RarceD/TFM--Bluetooth-Beacon-Tracking-/Technical project/Memmory/rarced_memmory.pdf

DOCUMENTO TÉCNICO

## SISTEMAS DE POSICIONAMIENTO DE OBJETOS MEDIANTE LA TECNOLOGÍA

## BLUETOOTH LOW ENERGY, MODO BEACON

27 de enero de 2021

Rubén Arce Domingo
Máster en automatización y robótica industrial
akimbo170@gmail.com

### Índice

1 Memoria descriptiva | 5
2 Memoria justificativa | 13
3 Planos | 21
4 Pliego de condiciones | 22
5 Presupuestos | 23
6 Bibliografía | 25

3

### Índice de figuras

1 | Detección de personas aplicando redes wifi | | 7
2 | Trama de bytes de cabecera de modo iBeacon (Apple) | | 8
3 | Modo Beacon Edison (Google) | | 9
4 | Diagrama explicativo de una red de ESP32 | 11
5 | Diagrama de GANTT del proyecto | 13
6 | Prueba de campo, medición Rssi de Beacons a 2 y 3 metros | 15
7 | Variaciones de Rssi entre beacons a distancias iguales | 16
8 | Trilataración con tres equipos escuchando al mismo Beacon | 16
9 | Posicionamiento de los beacons en carros de supermercado | 17
10 | Diferencia entre antena de media o cuarto de λ | 19
11 | Tipos de antena en función del espectro de emisión | 20
12 | Tipos de antena durante las pruebas de campo | 21

4

1 MEMORIA DESCRIPTIVA

### 1. Memoria descriptiva

### 1.1. Antecedentes y objeto del proyecto

Este proyecto surge como respuesta a la necesidad de poder localizar un número elevado de equipos en constante movimiento con exactitud en un espacio cerrado.

Los objetivos principales son los siguientes:

1. Estudiar las distintas alternativas para llevar a cabo el tracking de objetos de una forma sencilla y sin requerir de una gran inversión.
2. Analizar las tecnologías existentes para la monitorización en interiores.
3. Estudiar del parámetro Rssi como medida de la potencia de una señal y cálculo de la distancia entre equipos.
4. Desarrollar un sistema de visualización a través de un mapa sobre el que situar los equipos en movimiento.
5. Diseñar un hardware específico para la aplicación requerida.
6. Programar tanto el equipo emisor como el receptor, así como del algoritmo de visualización.
7. Comprobar el rendimiento del equipo y llevar a cabo pruebas de campo.

Una vez fijado el alcance del proyecto se puede empezar a planificar el mismo y buscar la mejor solución posible, por ello surgen los siguientes objetivos derivados de los primeros para poder sacar el producto al mercado:

1. Fijar un precio muy competitivo.
2. Desarrollar un producto estándar y de fácil aplicación.
3. Facilitar una instalación sencilla por un usuario no técnico.
4. Conseguir un mantenimiento escaso o nulo.
5. Producto seguro y que esté preparado para superar los marcados UL (Underwri-ters Laboratories) y CE (Conformidad Europea) así como protecciones frente a electricidad estática.

### 1.2. Ámbito de aplicación

El tracking de objetos en espacios cerrados está incrementando su popularidad debido a que es una arma de publicidad muy poderosa que demandan los grandes centros comerciales para llevar a cabo estudios de marketing y poder analizar el comportamiento de sus clientes.

BLE Tracking - 2021 | 5 | Rubén Arce

1.3 Análisis de soluciones al tracking de objetos | 1 MEMORIA DESCRIPTIVA

El mayor nicho de mercado es aplicado a no tener que interactuar tocando los objetos, esto, teniendo en cuenta los tiempos que corren, es una necesidad de numerosas empresas privadas, ayuntamientos y empresas estatales.

A modo de resumen se engloban los principales ámbitos de aplicación de esta tecnología:

1. Marketing: Estudios de mercado y de necesidad de los clientes. Elaboración de un "heat map", o mapa de las zonas con más afluencia de gente.
2. Sanidad: Monitorización de pacientes en planta.
3. Seguridad: Únicamente los empleados con autorización y proximidad podrán llevar a cabo acciones, esto tiene sentido a la hora de no tener que dar a cada trabajador una llave que pueda replicarse.
4. Vandalismo: Conociendo la localización de los equipos dentro de un local cerrado, en el momento en el que se deja de situar un elemento en el mapa, se puede dar la voz de alarma ante un robo.
5. Propaganda y nueva forma de publicidad: Activar acciones en función de la localización en determinados puntos de interés permite llevar a otro nivel las ideas de los publicistas.

Vemos por tanto que hay numerosas aplicaciones y una alta demanda de este producto tecnológico, es por ello por lo que se procede a explorar cual es la forma más adecuada para llevarlo a cabo e implementarlo.

### 1.3. Análisis de soluciones al tracking de objetos

Se plantean dos problemáticas, en primer lugar se busca llevar a cabo el seguimiento de elementos en movimiento, y por otro lado, se ha de enviar esta información de alguna forma al sistema correspondiente para que lleve a cabo el análisis de los datos. Esta última acción es esencial en el proceso, es lo realmente interesante desde el punto de vista del cliente final de esta tecnología. En lo que respecta a la obtención de datos de posición relativa de objetos o personas se presentan las siguientes opciones:

### 1.3.1. Wifi

Llevar a cabo el tracking mediante la escucha de wifis es una posibilidad, para ello sería necesario que, inicialmente, se colocara un móvil en cada uno de los objetos a identificar. Esto es aceptable en el caso de monitorización de personas pero inasumible para objetos.

El procedimiento consistiría en llevar a cabo un barrido de direcciones MACs que generan los móviles cuando tienen el wifi activado, es decir que este sistema no funcionaría en el caso de que una persona lleve puestos los datos del móvil únicamente.

BLE Tracking - 2021 | 6 | Rubén Arce

1 MEMORIA DESCRIPTIVA | 1.3 Análisis de soluciones al tracking de objetos

Otra desventaja es el hecho de que al tener un equipo buscando wifis la información personal del propietario, es decir, localización, fecha, hora a la que se intentó conectar y dirección MAC que identifica y relaciona un móvil a una persona, queda expuesta. Se ha de tener en cuenta la política de privacidad vigente, la cual se incumpliría al emplear esta tecnología para llevar a cabo el tracking.


Figura 1: Detección de personas aplicando redes wifi.

La única solución al problema es que se ha de pedir permiso formal a la persona para poder llevar a cabo el tratamiento de sus datos, cosa que es dificil puesto que se desconoce quien va a llevar a cabo el uso del equipo.

El artículo 29 de privacidad de datos de la comunidad europea dice lo siguiente: “WiFi-tracking, depending on the circumstances and purposes of the data collection, such tracking under the GDPR is likely either to be subject to consent, or may only be performed if the personal data collected is anonymised”. Es por ello por lo que se tendrá en cuenta como opción aunque haya numerosos puntos en contra para implementar un sistema como este.

### 1.3.2. GPS

La tecnología por excelencia para llevar a cabo el seguimiento de objetos o personas es el GPS. La principal desventaja que presenta es el elevado consumo energético comparado con el wifi o el bluetooth.

Mantener un módulo GPS encendido y pretender llegar a una autonomía de años es a día de hoy imposible, es por ello por lo que existen dos opciones. O se emplea un teléfono móvil para llevarlo a cabo, cosa inviable si se intentan monitorizar objetos y no personas en movimiento, o el tiempo de refresco de los datos ha de ser muy lento, del orden de horas, cosa de nuevo inasumible para la aplicación que se presenta.

Por otro lado, se ha de tener en cuenta también el aumento de precio que supondría un módulo GPS sumado a la antena que lleva consigo de dimensiones nada despreciables. Consecuentemente, esta tecnología se tendrá en cuenta pero no es la más adecuada para la problemática presente.

BLE Tracking - 2021 | 7 | Rubén Arce

1.3 Análisis de soluciones al tracking de objetos | 1 MEMORIA DESCRIPTIVA

### 1.3.3. Bluetooth Low Energy - Beacon

La tecnología Bluetooth es un estándar industrial aplicado a conexiones inalámbricas que permite transferir grandes cantidades de información en distancias cortas a bajas velocidades. Puede ser enfocado a conexión punto a punto, o como es nuestro caso llevar a cabo una red de equipos que emiten en modo broadcast.

La potencia de emisión va desde los -20 dBm (0.01 mW) hasta los +20 dBm (100 mW). Cuanta mayor potencia de emisión, mayor consumo energético del dispositivo, pero también conseguiremos una mayor distancia de escaneo.

La forma de envío de datos que más encaja dentro de la tecnología BLE (Bluetooth Low Energy) es Beacon o baliza, un dispositivo que transmite una señal de bluetooth cada cierto tiempo y es visible por cualquier otro equipo que escuche en esa misma frecuencia. La principal ventaja es que no es necesario llevar a cabo la conexión al equipo que escucha. Existen varios tipos de beacons:

1. iBeacon: Fue la primera tecnología BLE Beacon desarrollada por Apple. Permite leer y emitir en modo broadcast para cualquier dispositivo que disponga de Bluetooth low energy. Es un protocolo propietario, es decir es un estándar cerrado. Los iBeacons disponen de los siguientes identificadores:

UUID: Indentificador único del dispositivo, una cadena de carácteres de 16 bytes que permite caracterizar a cada equipo.

Major: Número entero de 0 a 65535, se usa para identificar grupos, un ejemplo sería asignar un Major común para todos los beacons de una misma planta o habitación.

Minor: Es también un número entero de 0 a 65535 que se emplea para distinguir un Beacon específico dentro de un grupo, entendiéndose como grupo aquellos beacons con mismo valor de Major.

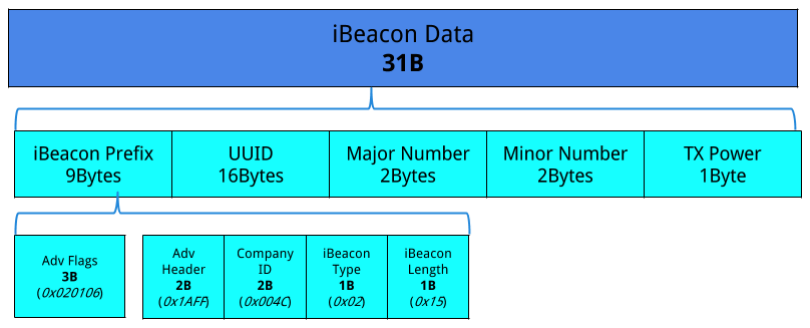
[picture p137: figure]

Figura 2: Trama de bytes de cabecera de modo iBeacon (Apple).

BLE Tracking - 2021 | 8 | Rubén Arce

1 MEMORIA DESCRIPTIVA | 1.4 Análisis de opciones de subida de datos
2. Eddystone: Creado por Google, es un protocolo de código abierto. A diferencia del protocolo anterior este permite transmitir:

URL: Un url propio de una web, de esta forma se evita la necesidad de tener que contar con una app instalada.

UID: Similar al UUID del iBeacon, este parámetro identifica al Beacon y permite llevar acciones individuales.

TML: Permite enviar información relativa al Beacon, como por ejemplo, el porcentaje de batería o valores de sensores.


Figura 3: Modo Beacon Edison (Google)

3. AltBeacon: Es un protocolo de código abierto que surge como resultado de las incompatibilidades de las dos tecnologías anteriores, la ventaja principal es que permite más flexibilidad de modificaciones así como compatibilidad entre sistemas operativos.

### 1.4. Análisis de opciones de subida de datos

Una vez exploradas las opciones de posicionamiento de los equipos se llevará a cabo el estudio de posibilidades de subida de estos datos a la nube, es por ello por lo que se contemplarán varias opciones:

### 1.4.1. MQTT

MQTT (Message Queing Telemetry Transport) es un protocolo estándar aplicado principalmente al IoT (Internet of Things). Está basado en publicación y suscripción con un servicio de mensajería push. Los mensajes se publican en topics, sobre los cuales los distintos dispositivos se encuentran escuchando. La base de la comunicación es el Broker, encargado de dar soporte a todos los topics, los clientes inician

BLE Tracking - 2021 | 9 | Rubén Arce

1.4 Análisis de opciones de subida de datos | 1 MEMORIA DESCRIPTIVA

una conexión TCP/IP con él que se mantiene abierta constantemente hasta que el cliente la finalice. Se emplean los puertos 1883 o 8883 con seguridad TLS. Cada mensaje tiene un QoS (Quality of service), es el mecanismo de calidad del servicio, o lo que es lo mismo es la forma de gestionar la robustez de los mensajes entre clientes y ante los fallos de conectividad.

QoS 0: Envío una única vez

QoS 1: Mensaje enviado hasta que se garantiza que se entrega.

QoS 2: Garantizado que cada mensaje se entrega al suscriptor por una única vez.

Esta es una opción para conseguir que los equipos que escuchan a los beacons envíen a un mismo topic la información obtenida por bluetooth. Será el sistema de visualiación el que esté escuchando también en el mismo topic.

### 1.4.2. HTTP Post

A través del protocolo de transferencia de hipertexto se puede llevar a cabo una petición post, la cual consiste en que un servidor acepte los datos recibidos por el microcontrolador. La ventaja es que con el HTTP post solo se mantiene la conexión abierta al hacer la conexión, luego se desconecta hasta la siguiente vez en la que se vuelvan a publicar datos.

Otra ventaja es que mediante peticiones se pueden transferir datos a distintos servidores. Por el contrario, con MQTT solo se puede enviar información a aquellos servidores que estén suscritos al mismo tópic que el dispositivo.

El principal inconveniente es que está demostrado que en una red 3G, una petición post es del orden de 93 veces más lenta que un mensaje MQTT, con el consiguiente consumo energético que esto conlleva. Otro inconveniente es el hecho de que se requiera de un servidor con una API o endpoint que esté constantemente escuchando a los distintos posts.

### 1.4.3. ESP Now

Se plantea la opción de que no todos los equipos que escuchan a los beacons dispongan de conexión a internet, es por ello por lo que se baraja la posibilidad de llevar a cabo una red de elementos que escuchan y que envían a un único concentrador encargado de enviar esta información a internet por cualquier otro método. Es decir, se contempla la opción de establecer una red de elementos que escuchan, para lo cual se emplea un protocolo de comunicación rápido denominado ESP-NOW, que tiene las siguientes características:

BLE Tracking - 2021 | 10 | Rubén Arce

1 MEMORIA DESCRIPTIVA | 1.5 Resultados finales

Encriptación de las comunicaciones.

Hasta 250 Bytes de payload o mensaje a enviar.

Rapidez de comunicación entre microcontroladores.

La idea sería la siguiente:

a) El equipo que lleva a cabo el barrido y búsqueda de beacons escanea e intenta conectarse a internet por wifi.
b) Si lo consigue publica los datos, en el caso de que falle enviará por ESP NOW la información que no puede subir a internet a otro equipo en su misma red que si que pueda.
c) Este segundo hará lo mismo hasta que finalmente alcance con uno que sí que pueda subir estos datos.

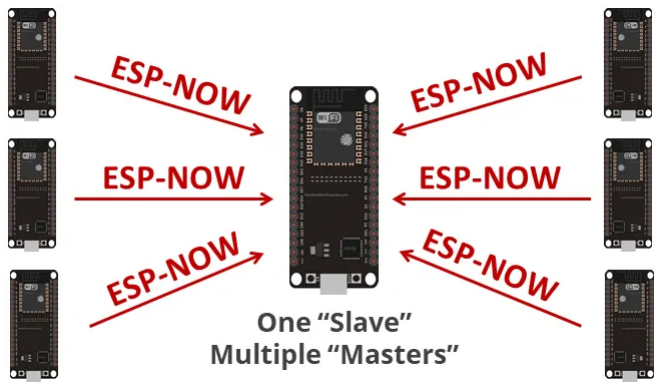
[picture p138: figure]

Figura 4: Diagrama explicativo de una red de ESP32.

### 1.5. Resultados finales

Una vez analizadas las dos problemáticas y las distintas soluciones a cada una de ellas, se ha confeccionado la siguiente tabla en la que se puede ver una comparativa entre cada una de ellas.
Por un lado está la forma en la que poder medir las distancias de los equipos con respecto a los equipos que escuchan, se contemplan las siguientes opciones:
Tecnología | Coste | Complejidad | Distancia | Consumo energético
GPS Wifi Bluetooth | Elevado Medio Bajo | Baja Media Media | Ilimitada 100 m 100 m | Muy alto Alto Muy bajo

El claro ganador en este caso es el Bluetooth, debido, principalmente, al precio que supondría llevar a cabo una red de estas características, así como el bajo consumo energético que hace que el mantenimiento de los equipos sea casi inexistente.

BLE Tracking - 2021 | 11 | Rubén Arce

1.6 Planificación | 1 MEMORIA DESCRIPTIVA

Recordemos que una de las premisas iniciales era que los equipos requieran poco cuidado por parte del cliente, lo que se consigue empleando esta tecnología en la que solo es necesario cambiar una pila una vez al año.

En lo que respecta a la comunicación de estos datos de distancia entre equipos a internet, se ha reunido de nuevo en la siguiente tabla un resumen con las opciones y los puntos a favor y en contra de cada una de las tecnologías.

Tecnología | Velocidad de datos | Coste | Complejidad
MQTT HTTP POST ESP NOW | Elevada Baja Media | No Medio No | Baja Baja Alta

La elección en este caso está mucho más ajustada, en el caso de que se pueda conectar a todos los equipos que escuchan a internet el ganador será la opción de MQTT, puesto que es la forma más fácil de llevar a cabo el envío de datos.

Si que no llegara la señal wifi a todos los puntos en los que se decida llevar a cabo el tracking de objetos surge un problema puesto que perderemos esos datos. La solución es hacer que este equipo, que no tiene conexión a internet, envíe los datos por ESP NOW a otro que si que sea capaz de subir tanto su información como la de su compañero al broker por MQTT.

Puesto que se pretende llevar a cabo un sistema válido para toda la casuística de instalaciones, se han contemplado ambas opciones y la implementación real llevará a cabo los dos métodos.

Es decir, que la única opción desechada ha sido la conexión directa con un servidor mediante HTTP debido a que, en primer lugar sería necesario programar un servicio que escuchará en este endpoint y luego sería necesario hostearlo para que disponga de una IP pública estática y sea accesible desde cualquier parte del mundo.

### 1.6. Planificación

Para sintetizar el proceso de desarrollo del proyecto técnico se empleará un diagrama GANTT. En la figura 5 podemos ver la evolución del desarrollo del mismo así como la duración exacta de cada etapa.

BLE Tracking - 2021 | 12 | Rubén Arce

2 MEMORIA JUSTIFICATIVA

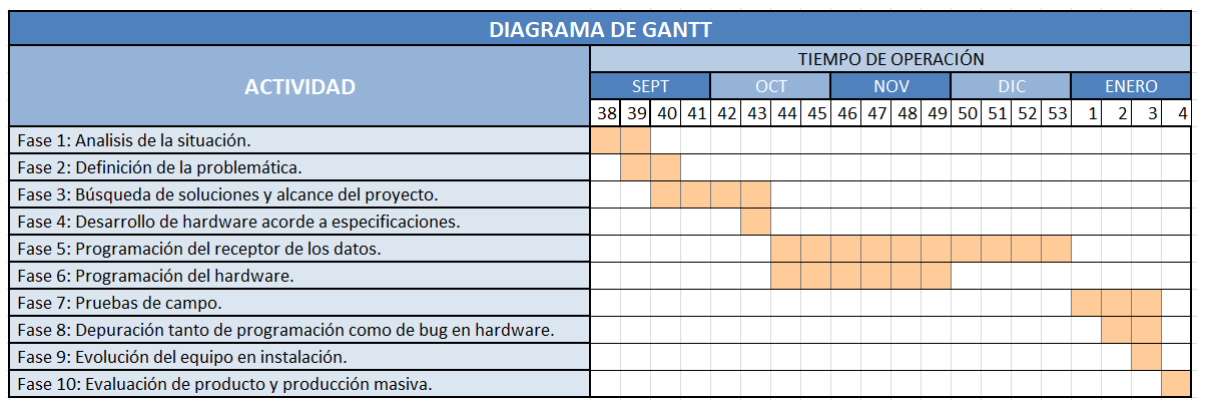
[picture p139: figure]

Figura 5: Diagrama de GANTT del proyecto.

### 2. Memoria justificativa

### 2.1. Cálculos justificativos de la instalación

En este apartado se llevará a cabo el estudio de la viabilidad del proyecto desde el punto de vista técnico, para lo cual se contemplará un estudio del Rssi como forma de medir distancia, un análisis de la previsión energética de los equipos, un análisis del las frecuencias y ganancias de las antenas empleadas.

### 2.2. Cálculo de distancia por Rssi

### 2.2.1. Rssi

El Rssi (Received signal strength indicator) es un indicador de la energía o potencia recibida en un mensaje de radio. Está asociado con la atenuación de la señal, cuanto más pequeña es su valor menor atenuación. Este valor está presente no solo en Bluetooth sino también en el Wifi (2,4 GHz) o en las bandas de radio industriales, científicas y médicas, las denominadas ISM (desde 433MHz a 458.5MHz y desde 860MHz a 960MHz)

De las muestras obtenidas en pruebas de campo con bluetooth se puede concluir que es posible llegar a estimar la distancia a partir de los valores de Rssi con un error que disminuye cuanto más alejados se encuentren los elementos a medir.

Los rangos del Rssi se obtienen bien por aproximaciones teóricas o bien por experi-mentación. Esto es debido a que es fuertemente alterado por las condiciones del medio en el que se encuentre. Asimismo es importante mencionar que este parámetro es medido a través de un hardware que rara vez tiene un comportamiento idéntico, eso explica las fluctuaciones también.

BLE Tracking - 2021 | 13 | Rubén Arce

2.2 Cálculo de distancia por Rssi | 2 MEMORIA JUSTIFICATIVA

Los modelos de cálculo del Rssi se basan en la pérdida de señal en el espacio, como sabemos la potencia de la señal disminuye con el cuadrado de la distancia. Esta ecuación de Friis para la transmisión libre en el espacio es una fórmula teórica, existen aproximaciones obtenidas por métodos empíricos:

PL(d)[dB] = PL(d0)[dB] + 10n ∗ log10

di
d0

(1)

Siendo PL (d0) la pérdida de propagación a 1 metro y n una constante que depende del medio, será igual a 2 si se encuentra en el espacio libre sin obstáculos ni reflexiones o dispersiones de señal.

Para calcular este parámetro n se ha de aplicar la siguiente fórmula, como podemos ver para llevar a cabo el cálculo se han de tomar valores empíricos de potencias:

n =

PL(di) − PL(d0)
10n ∗ log di
d0

(2)

Por lo tanto, y una vez obtenidos los valores de potencia a distintas distancias, podemos obtener la ganancia de la señal recibida:

Rssi[dBm] = −10n ∗ log10 d + A[dBm] | (3)

Disponiendo ya del valor de la constante de pérdidas, d, calculado con la ecuación
(2) y los valores de Rssi medidos desde la antena receptora a 1 metro de distancia, (3), podemos obtener:

d = 10

−(Rssi−A)
10n | (4)

Llevados a cabo los cálculos por parte del equipo que escucha a los distintos beacons, podemos calcular la distancia real a cada uno de ellos. En el caso de que se solapen y dos receptores escuchen el mismo Beacon será necesario llevar a cabo el proceso de trilateración expuesto a continuación. Para comprobar la fluctuación del parámetro del Rssi se ha llevado a cabo la toma de este parámetro a lo largo de un periodo de tiempo largo y los resultados a 2 metros y a 3 metros se encuentran respectivamente en la figura 6.
Podemos ver que hay pequeñas flucuaciones y es por ello por lo que será necesario implementar un sencillo filtro para evitar el ruido electromagnético que hemos visto anteriormente.
Se ha llevado a cabo la prueba de incrementar el número de iBeacons y situarlos a la misma distancia del equipo que escucha, los resultados se muestran en la figura 7. Análogamente las diferencias son notables, esto demuestra la necesidad de implementar un filtro que no falsee las medidas y cree distancias incoherentes puntuales entre los equipos.
BLE Tracking - 2021 | 14 | Rubén Arce

2 MEMORIA JUSTIFICATIVA | 2.2 Cálculo de distancia por Rssi

El filtro más habitual para este tipo de aplicaciones es el denominado Kalman Filter:

Rssisuavizado = α ∗ Rssin + (1 − α) ∗ Rssi(n−1) | (5)

Otra opción que experimentalmente ha dado buenos resultados es la de selecionar los 20 valores anteriores, obtener la media y si se separa más de un 40 % el valor nuevo lo rechazo. Con esto consigo eliminar las fluctuaciones indesadas que se podían apreciar en la figura 6.

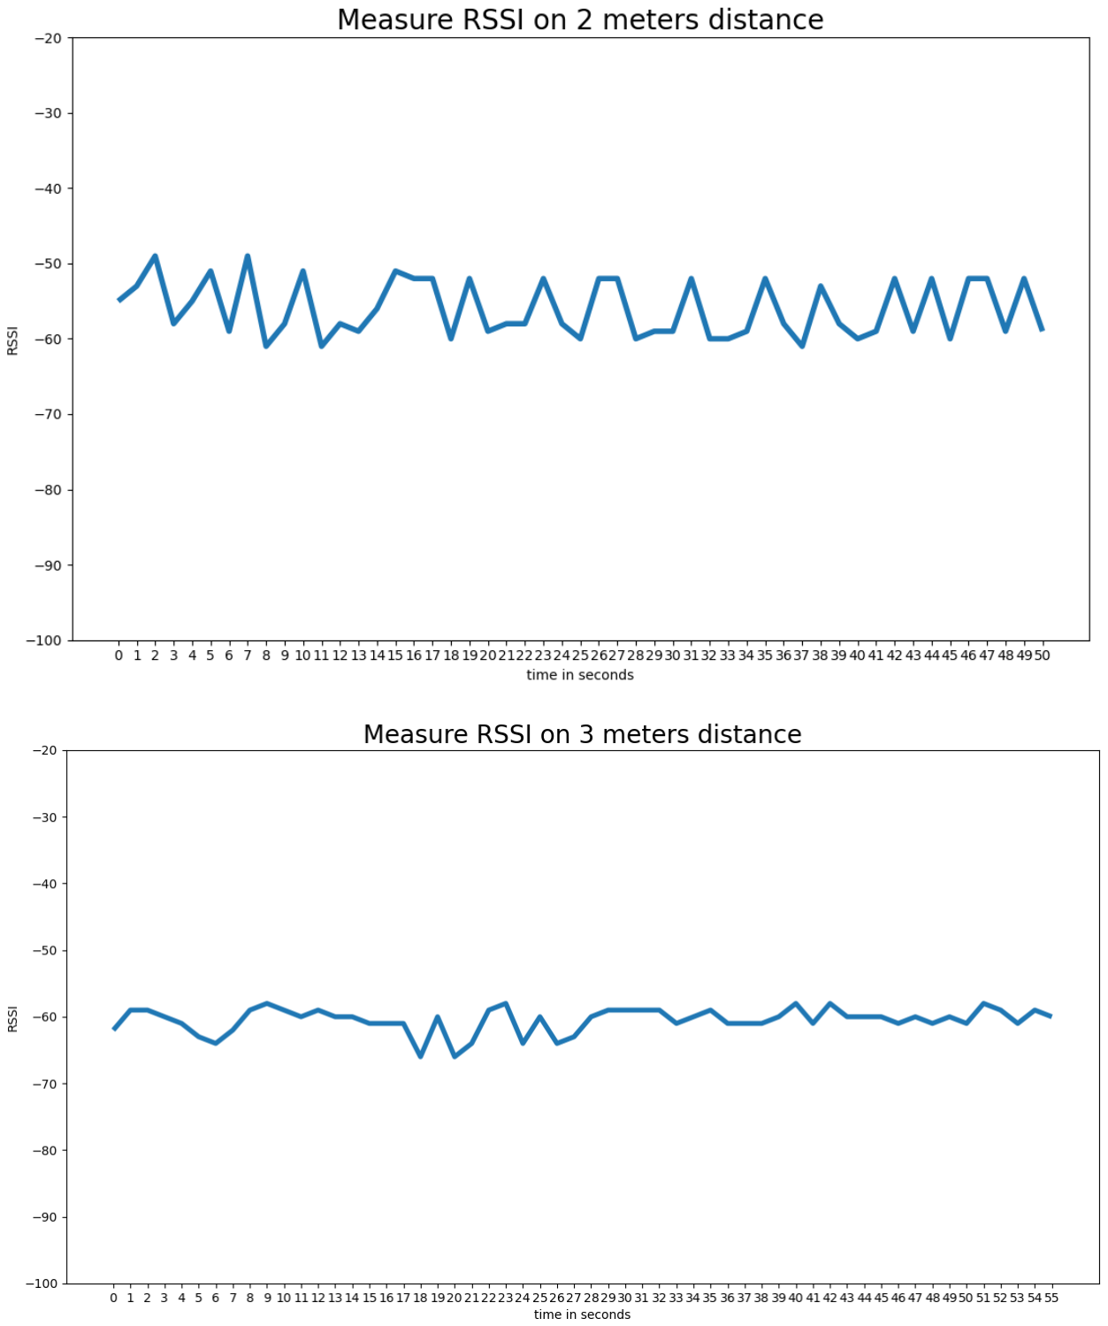
[picture p140: figure]

Figura 6: Prueba de campo, medición Rssi de Beacons a 2 y 3 metros.

### 2.2.2. Trilateración y posicionamiento

Una vez obtenidas las distancias a los distintos equipos de receptores es necesario llevar a cabo el posicionamiento exacto de los mismos, para ello se emplea la trilateración:

BLE Tracking - 2021 | 15 | Rubén Arce

2.2 Cálculo de distancia por Rssi | 2 MEMORIA JUSTIFICATIVA


Figura 7: Variaciones de Rssi entre beacons a distancias iguales.


Figura 8: Trilataración con tres equipos escuchando al mismo Beacon.

Hemos de resolver las siguientes ecuaciones básicas sobre la distancia entre recta y un punto en una circunferencia, en la figura 8 podemos verlo gráficamente.

dA1 =

q
(x − xA)

2 + (y − yA)

2 | (6)

dB1 =

q
(x − xB)

2 + (y − yB)

2 | (7)

dC1 =

q
(x − xC)

2 + (y − yC)

2 | (8)

Llevando a cabo la simplificación obtenemos un sistema de ecuaciones que permite calcular la distancia relativa a cada uno de los equipos que escuchan. En el anexo de software se muestran los resultados con mayor detalle. En la figura 9 podemos ver un adelanto del posicionamiento de carros de la compra en un supermercado.

BLE Tracking - 2021 | 16 | Rubén Arce

2 MEMORIA JUSTIFICATIVA | 2.3 Cálculo de consumos energéticos


Figura 9: Posicionamiento de los beacons en carros de supermercado.

### 2.3. Cálculo de consumos energéticos

El procesador empleado, tanto para el equipo emisor como para el receptor, disponen de los siguientes modos de funcionamiento:

Active Mode: 160-260mA. Los dos cores del procesador encendidos, así como el procesador ULP, RTC, Wifi, Bluetooth, Radio, Peripherals.

Sleep mode: 3-20mA. Activos los dos cores, el coprocesaror ULP coprocessor y el RTC, inactivos el Wifi, Bluetooth, Radio y periféricos.

Light sleep mode: La CPU está pausada apagando los pulsos de su reloj interno, sin embargo, el RTC y el coprocesador ULP se mantienen activos. Esto supone un consumo menor que en los anteriores modos de funcionamiento, se puede llegar a los 0.8mA.

Deep sleep mode: tanto la CPU como gran parte de la RAM, así como todos los periféricos se mantienen apagados. Las únicas parte no apagadas son los RTC de los periféricos y de la CPU (incluyendo el ULP) y su memoria interna. El chip consume en torno a los 0.15 mA si se mantiene encendido el ULP y 10µA si no. En el modo deep sleep todo se encuentra apagado, por ello los datos de la memoria del rtc se pierden puesto que se encuentra en reinicio el uC.

Hibernation mode: A diferencia del modo deep sleep el oscilador de 8MHz y el ULP se encuentran apagados, no es posible almacenar nada de información. Tan solo el RTC funcinando con el reloj de baja velocidad puede funcionar. En este modo de funcionamiento el micro consume sobre los 2.5µA.

BLE Tracking - 2021 | 17 | Rubén Arce

2.4 Cálculo de ganancia de antenas | 2 MEMORIA JUSTIFICATIVA
Modo del ESP32 | Consumo energético
Wi-Fi Tx a 13dBm 21dBm Wi-Fi/BT Tx a packet 0dBm Wi-Fi/BT Rx and listening Sleep mode Light sleep mode Deep sleep mode Hibernation mode | 160 260mA 120mA 80 90mA 3-20mA 0,8mA 0,15 mA - 10µA 2,5µA

A la hora de llevar a cabo la decisión sobre cómo llevar a cabo el protocolo de comunicación se ha de tener en cuenta el consumo de los equipos, en especial en lo que respecta a los beacons.

Es por ello por lo que se ha optado por dormir al equipo durante 58 segundos, despertarlo, enviar su trama bluetooth y luego dormirlo hasta la siguiente vez que despierte. Con esto conseguimos un consumo que varía en función de la frecuencia de envío. En las siguiente tablas se puede ver un análisis en función del tiempo y en consecuencia la duración media de las baterías. Se ha puesto como ejemplo una frecuencia de envío de 10 minutos.

Frecuencia de envío | Consumo energético
1 min 5 min 10 min 15 min 30 min | 2,415 mA 0,495 mA 0,255 mA 0,175 mA 0,095 mA
Tipo de batería | Capacidad (mAh) | Autonomía(días) f=10 min | Autonomía(días) f=5 min
Pila CRC 2032 Pila AA Batería Li-Ion | 240 mAh 2500 mAh 1600 mAh | 39 409 261 | 20 210 135

Podemos ver por lo tanto como con una pila AA se podría llegar a conseguir sin problemas una autonomía de casi un año, es por esta razón y por el tamaño reducido por lo el que se va a optar por esta solución.

### 2.4. Cálculo de ganancia de antenas

Una antena convierte la enegía electrica del transmisor en energía electromagnética y viceversa, las antenas pueden ser para recibir, para transmitir o ambas. La localización de la antena, las dimensiones y el diseño pueden afectar drásticamente en el funcionamiento óptimo de la red de beacons. Las antenas típicas en aplicaciones de radiofrecuencia con bluetooth son de -10dBm a 10dBm.

BLE Tracking - 2021 | 18 | Rubén Arce

2 MEMORIA JUSTIFICATIVA | 2.4 Cálculo de ganancia de antenas

El denominado path loss o atenuación de la señal de radio es la reducción de la densidad de potencia de una onda durante la propagación en el espacio. Este parámetro es esencial a la hora de poder establecer una red de bluetooth de estas dimensiones. Las dimensiones de la antena se pueden llegar a obtener mediante:

f(Hz) = v(m/s)
λ(m)

(9)

λ0(m) = v0(m/s)
f(Hz)

=

2, 998 ∗ 10⁸
2, 4 ∗ 10⁹
= 12, 49cm | (10)

Para la aplicación que tenemos existen dos tipos de antenas:

Antenas monopolo λ/4: Menor tamaño pero menor eficiencia.

Antenas dipolo λ /2: Mayor tamaño pero mejores resultados.

Teniendo en cuenta que esta antena estará en una caja más grande y a la vista el tamaño no será un limitante. A modo de ejemplo en la figura 10 se muestra como es internamente cada una de las antenas.

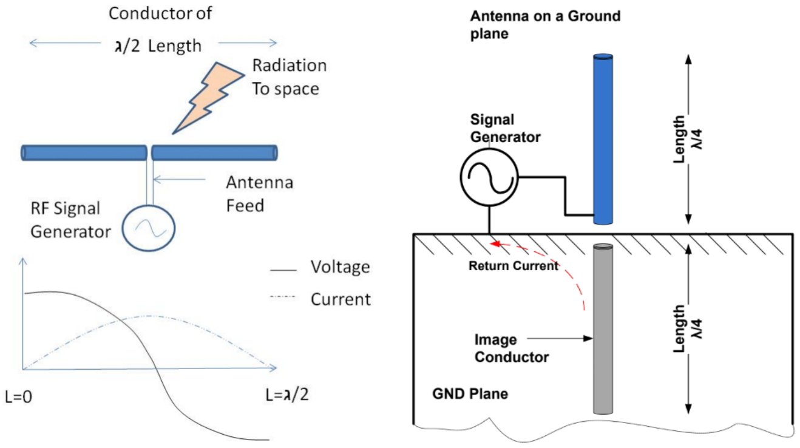
[picture p141: figure]

Figura 10: Diferencia entre antena de media o cuarto de λ.

Además se ha de tener en cuenta que las antenas atienden a su diagrama de radiación, es decir, al espectro tridimensional de emisión. Según la forma de radiación podemos distinguir.

Antenas isotrópica: Emite con la misma densidad en todas las direcciones.

BLE Tracking - 2021 | 19 | Rubén Arce

2.4 Cálculo de ganancia de antenas | 2 MEMORIA JUSTIFICATIVA

Antenas omnidireccionales: Emite en torno a un solo plano isotrópico.

Antena directiva: Concentra la energía radiada en tan solo una dirección del espacio.

En la figura 11 podemos ver los lóbulos de emisión y recepción de radiofrecuencia de las distintas antenas.

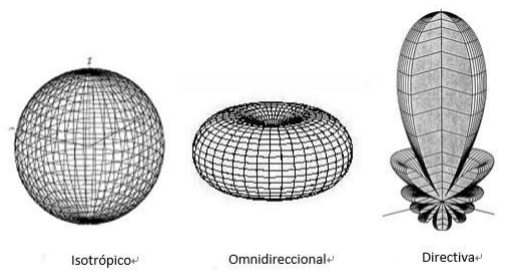
[picture p142: figure]

Figura 11: Tipos de antena en función del espectro de emisión.

Dentro del mundo de las antenas existen numerosos modelos y opciones que se enumeran a continuación:

1. Antenas de cable: son las más sencillas de todas y como su propio nombre indica es un simple cable soldado a la PCB de una dimensión determinada, la cual se corresponde con la de una antena monopolo λ/4. El cable aporta el mayor rendimiento y rango de radiofrecuencia debido a sus dimensiones y a su caracter flexible, moldeable y orientable sin importar la posición de la tarjeta.
2. Antena PCB: es una pista en el propio circuito impreso que puede tener numerosas formas, a diferencia de la de cable esta solo se encuentra en el espacio 2D. Tiene menos eficiciencia que las anteriores y requiere más espacio pero son incluso más baratas.
3. Antena de chip: este tipo de antena es una tarjeta o módulo que ocupa menos espacio que cualquiera de las anteriores y tiene un rendimiento intermedio entre ambas otras dos opciones.

Por otro lado, se han llevado pruebas de campo con distintos modelos y distintas posiciones dentro de la caja, a continuación se muestran las antenas con las que se han llevado a cabo las pruebas reales en la figura 12.

BLE Tracking - 2021 | 20 | Rubén Arce

3 PLANOS

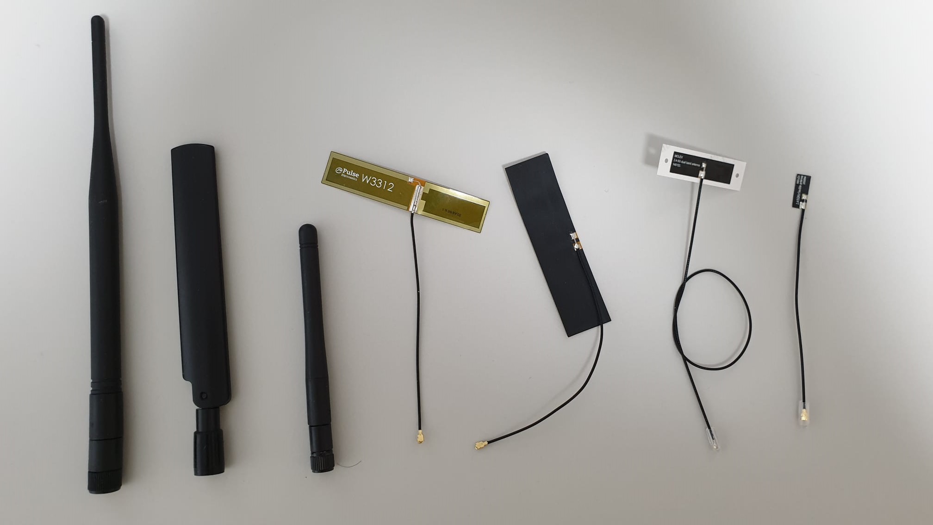
[picture p143: figure]

Figura 12: Tipos de antena durante las pruebas de campo.

Las conclusiones obtenidas son que las antenas pcb de λ /2 obtienen más uniformidad en las medidas a igual distancia, mientras que las antenas de cable ofrecen mayor rango pero son menos discretas. En definitiva, la antena es algo esencial y más allá del modelo elegido prioriza más el hecho de que todos los equipos de la red dispongan de exactamente el mismo diseño.

### 3. Planos

### 3.1. Planos mecánicos

Los planos catalogados como mecánicos hacen referencia a la estructura de plástico que sostiene y protege a la electrónica de las condiciones ambientales y de contacto directo con las personas.
En el anexo de diseño mecánico se especifica con mayor detalle el procedimiento y el prototipado con impresora 3D. A este respecto se presentan dos planos:

Chasis de receptor o gateway

Chasis de emisor o Beacon

### 3.2. Planos eléctricos

Los circuitos eléctricos de la electrónica desarrollada que se presentan son los siguientes:

Esquemático del emisor Beacon y esquemático del receptor ESP32

PCB circuito del emisor Beacon y PCB circuito del receptor ESP32

En en el anexo de diseño eléctrico se explican con mayor detalle.

BLE Tracking - 2021 | 21 | Rubén Arce

4 PLIEGO DE CONDICIONES

### 4. Pliego de condiciones

### 4.1. Prescripciones ténicas generales

### 4.1.1. Normativa relativa a radiofrecuencia

Real Decreto 123/2017: de 24 de febrero, por el que se aprueba el Reglamento sobre el uso del dominio público radioeléctrico.

Real Decreto 188/2016: de 6 de mayo, por el que se aprueba el Reglamento por el que se establecen los requisitos para la comercialización, puesta en servicio y uso de equipos radioeléctricos, y se regula el procedimiento para la evaluación de la conformidad, la vigilancia del mercado y el régimen sancionador de los equipos de telecomunicación.

Orden IET/614/2015: de 6 de abril, por la que se modifica la Orden IET/787/2013, de 25 de abril, por la que se aprueba el cuadro nacional de atribución de frecuencias.

Esto viene recogido en la orden ERC/DEC/(01)07.

Ley 9/2014: de 9 de mayo, General de Telecomunicaciones.

Orden CTE/23/2002: de 11 de enero, por la que se establecen condiciones para la presentación de determinados estudios y certificaciones por operadores de servicios de radiocomunicaciones.

### 4.1.2. Normativa relativa a bluetooth y wifi

Se ha de tener en cuenta que para poder emplear dispositivos bluetooth se ha de respetar los estándares

IEEE 802.15.1 define Bluetooth 1.x, que puede alcanzar velocidades de 1 Mbps;

IEEE 802.15.2 recomienda prácticas para utilizar la banda de frecuencia de 2.4 GHz (en convivencia con el wifi)

IEEE 802.15.3 ofrece velocidades de banda ancha (20 Mbps) con Bluetooth;

IEEE 802.15.4 es un estándar que define el nivel físico y el de control de acceso al medio para redes de área personal con tasas bajas de datos (low-rate wireless personal area network, LR-WPAN).

La clase del disposivo que queda recogida en la siguiente tabla es también un dato a tener en cuenta puesto que no se les aplica la misma normativa.

Clase | Potencia | Alcance aproximado
Clase 1 Clase 2 Clase 3 Clase 4 | 100 mW / 20 dBm 2,5 mW / 4 dBm 1 mW / 0 dBm 0,5 mW / -3 dBm | 100 m 5 - 10 m 1 m 0,5 m
BLE Tracking - 2021 | 22 | Rubén Arce

5 PRESUPUESTOS

En nuestro caso y teniendo en cuenta la aplicación, se ha optado por emitir por debajo de los 20 dBm de tal forma que no se aplica apenas normativa, debido a que la potencia isotrópica radiada equivalente total será inferior a 100 mW.

### 5. Presupuestos

### 5.1. Precios unitarios

La tabla de precios se va a elaborar en distintas unidades que corresponden al precio por separado de cada una de las PCBs que se han diseñado.

### 5.2. Presupuestos parciales

### 5.2.1. Placa de circuito impreso emisor Beacon

Componente | Cantidad | Precio unitario
Resistencia metálica SMD 0805 1k 10 Resistencia metálica SMD 0805 10k 10 Condensador cerámico SMD 0805 0,1uF Condensador cerámico SMD 0805 10uF Regulador tensión LDO AMS1117-3.3V Microcontrolador ESP32-WROOM-32D Led SMD 0805 verde Led SMD 0805 rojo Led SMD 0805 naranja Batería Litio Ion | 1 1 1 1 1 1 1 1 1 1 | 0,009 € 0,009 € 0,005 € 0,016 € 0,098 € 2,840 € 0,013 € 0,013 € 0,015 € 1,520 €
TOTAL | 1 | 4,009 €
BLE Tracking - 2021 | 23 | Rubén Arce

5.3 Presupuestos total | 5 PRESUPUESTOS

### 5.2.2. Placa de circuito impreso receptor o gateway

Componente | Cantidad | Precio unitario
Resistencia metálica SMD 0805 1k 10 Resistencia metálica SMD 0805 10k 10 Condensador cerámico SMD 0805 0,1uF Condensador cerámico SMD 0805 10uF Regulador tensión LDO AMS1117-3.3V Microcontrolador ESP32-WROOM-32D Led SMD 0805 verde Led SMD 0805 rojo Led SMD 0805 naranja Pinheader conector para programación UART-TTL herramienta de dasarrollo Power Module AC-DC HI-LINK 3.3V Screw terminal P=5.08mm USB Mini B Female JST Connector P=2mm Jumper connector | 1 1 1 1 1 1 1 1 1 1 1 1 1 1 1 1 | 0,009 € 0,009 € 0,005 € 0,016 € 0,098 € 2,840 € 0,013 € 0,013 € 0,015 € 0,113 € 1,540 € 2,830 € 0,097 € 0,108 € 0,039 € 0,017 €
TOTAL | | 7,763 €

### 5.2.3. Desarrollo e instalación

Componente | Cantidad (h) € | Precio unitario
Diseñador hardware placas circuito impreso Desarrollador software sistema embebido Programador full stack web developer | 10 350 100 | 50 40 50

### 5.3. Presupuestos total

El presupuesto total se compone de la suma de los presupuestos parciales:

Unidad | Cantidad | Precio
Placa de circuito impreso Beacon o emisor Placa de circuito impreso receptor o gateway Desarrollo e instalación | 10 4 1 | 40 50 35
Total | IVA 21 % | 635€ 133,35 € 768,35€

Por lo tanto el presupuesto total con iva asciende a la cantidad de 1234123 4123 y veintimeil euros.

BLE Tracking - 2021 | 24 | Rubén Arce

6 BIBLIOGRAFÍA | 5.4 Factores económicos y financieros

### 5.4. Factores económicos y financieros

Para llevar a cabo el estudio de viabilidad económica se ha confeccionado la siguiente tabla donde podemos ver los flujos de caja así como la inversión inicial del proyecto:

- | Periodo 0 | Periodo 1 | Periodo 2 | Periodo 3
Inversión/gastos Flujos de caja | 1.200,00 € -1.200,00 € | 4.523,60 € 1.776,40 € | 4.523,60 € 3.476,40 € | 4.523,60 € 476,40 €

Se ha de tener en cuenta que esto es un proyecto real y que los gastos son verídicos y surgen del pago de las cuotas de autónomos, electricidad y gasolina que supone trabajar desde casa. Con todo esto y fijando una cuota de COK o coste de oportunidad de capital o mínima rentabilidad admisible para afrontar la realización del proyecto, se ha establecido de un 3 %.

### 5.4.1. TIR y VAN

El análisis de la tasa de interés de retorno y del valor actual neto son los que se recogen en la siguiente tabla:

TIR | 4.237,47 €
VAN | 164 %

Teniendo en consideración todos los aspectos menciones, se puede concluir que la inversión es rentable y asumible si se presupone una venta anual de proyectos con diferentes características. Es importante mencionar que este escenario no es real al 100 % debido a que no solo se venderá este producto, igualmente al ser ventas puntuales no se requiere un posterior tratamiento con el cliente y esto hace que sea más rentable.

### 6. Bibliografía

Accent systems. (s.f.). accent systems. https://accent-systems.com/es/producto/ibks-105/

Apple. (2014). Getting Started with iBeacon [version 1.0].

Bluetooth. (s.f.). Blueetooth. https://www.bluetooth.com/

Cejas, A. y Chardon, A. (2019). Algoritmos avanzados de posicionamiento en interiores

Chruszczyk, L. y Zajac, A. (2016). Comparison of Indoor/Outdoor, RSSI-Based Positioning Using 433, 868 or 2400 MHz ISM Bands. Intl Journal of Electronics and Telecommunications, 32(4), 395-399.

ESP-IDF Release V4.2. (2020, 7 de diciembre). Expressif loT Development Frame-work. Espressif. https://github.com/espressif/esp-idf

BLE Tracking - 2021 | 25 | Rubén Arce

6 BIBLIOGRAFÍA

Espressif Systems. (2020). ESP32 Hardware Design Guidelines [version 3.0].

Espressif Systems. (2020). ESP32 Technical Reference Manual [version 4.3].

Jayakody, J. A., Lokuliyana, S., Chathurangi, D. y Vithana, D. (2016). Indoor Positioning: Novel Approach for Bluetooth Networks using RSSI Smoothing. International Journl of Computer Applicatios, 137(13), 26-32.

Jefatura del Estado. (2014, 5 de mayo). Ley 114. Por la que se expide la Ley General
de Telecomunicaciones. BOE-A-2014-4950. https://www.boe.es/buscar/act.php?id=BOE-A-2014-4950

Ministerio de Ciencia y Tecnología de España. (2002, 11 de enero). Orden CTE/23/2002. Por la que se establecen condiciones para la presentación de determinados estudios
y certificaciones por operadores de servicios de radiocomunicaciones. BOE-A-2002-
694. (https://www.boe.es/diario_boe/txt.php?id=BOE-A-2002-694)

Nordic Semiconductor. (2017). nRF52832 Product Specification v1.4.

Pattnayak, T. y Thanikachalam, G. (2018). Antenna Design and RF Layout Guidelines [application notes]. Cypress. http://www.cypress.com/go/AN91445

Shang, F., Su, W., Wang, Q., Gao, H. y Fu, Q. (2014). A Location Estimation Algo-rithm Based on RSSI Vector Similarity Degree. International Journal of Distributed Sensor Networks. http://dx.doi.org/10.1155/2014/371350

ShareLaTeX. (s.f.). ShareLaTeX. https://www.sharelatex.com/

Shezhen Radioland Technology. Bluetooth Smart Module BLE4.0 NRF51822-Beacon Datasheet.

Tabibi, M. A. y Shahnewaz, A. (2012). RSSI Based Location [tesis de maestría, Universidad Politécnica de Milán].

utilizando la combinación de distintos tipos de sensores [trabajo de fin de grado, Universidad Nacional del Centro de la Provincia de Buenos Aires].

Vara, N., Poletto, G.A., Cáceres, M. y Busso, A. J. (2015). Cálculo de distancia entre los nodos de una red inalámbrica Zigbee en función del parámetro RSSI. Extensionismo, innovación y trasferencia tecnológica. Claves para el desarrollo, 2, 8-13.

Yu, X. (2014). Diseño de antenas de tipo parche para un transceptor WiMAX basado en el chip MAX2838 [trabajo fin de grado, Escuela Politécnica Superior de la Universidad Autónoma de Madrid].

BLE Tracking - 2021 | 26 | Rubén Arce
