RarceD/TFM--Bluetooth-Beacon-Tracking-/Technical project/Memmory/images/2s_ble_scanner_comparative_send.PNG

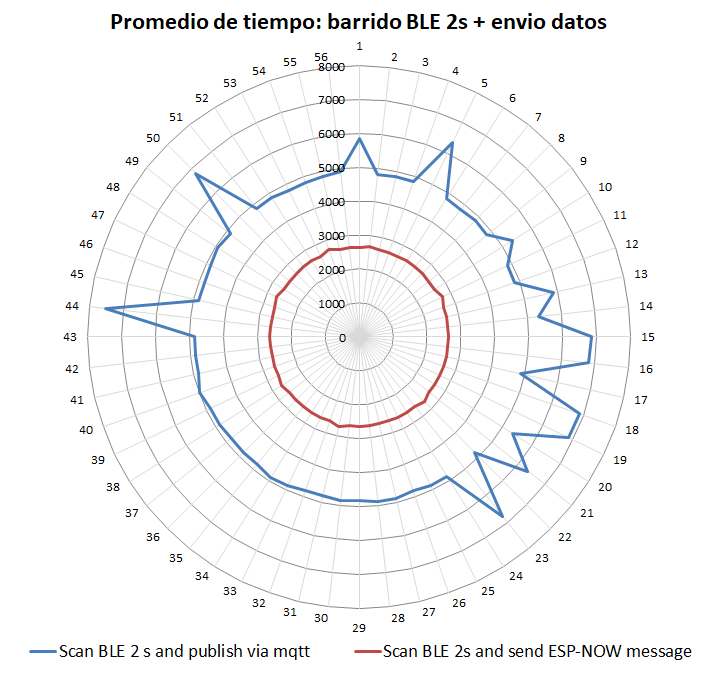
Technical project/Memmory/images/2s_ble_scanner_comparative_send.PNG
