RarceD/TFM--Bluetooth-Beacon-Tracking-/Technical project/Memmory/images/comparativa_ble_wifi_frecuencias.PNG

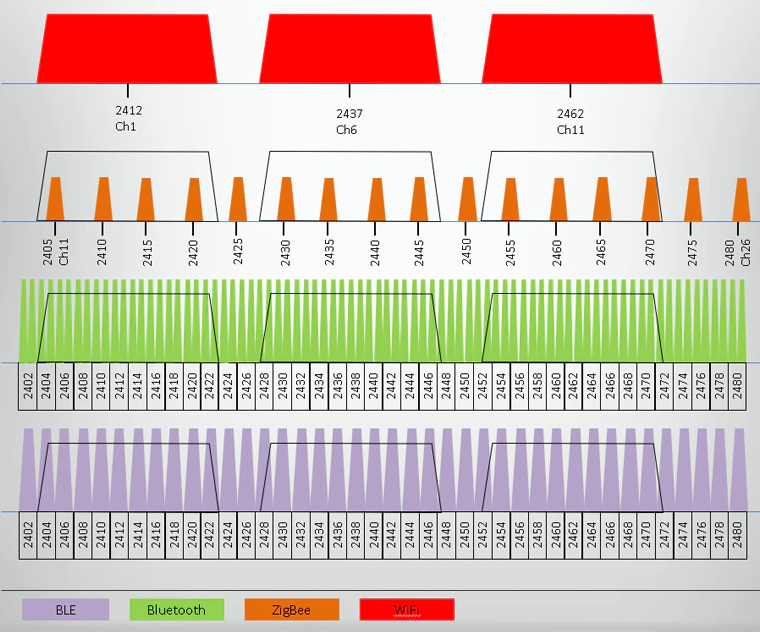
Technical project/Memmory/images/comparativa_ble_wifi_frecuencias.PNG
