RarceD/TFM--Bluetooth-Beacon-Tracking-/Technical project/Memmory/images/supermarket_1.PNG

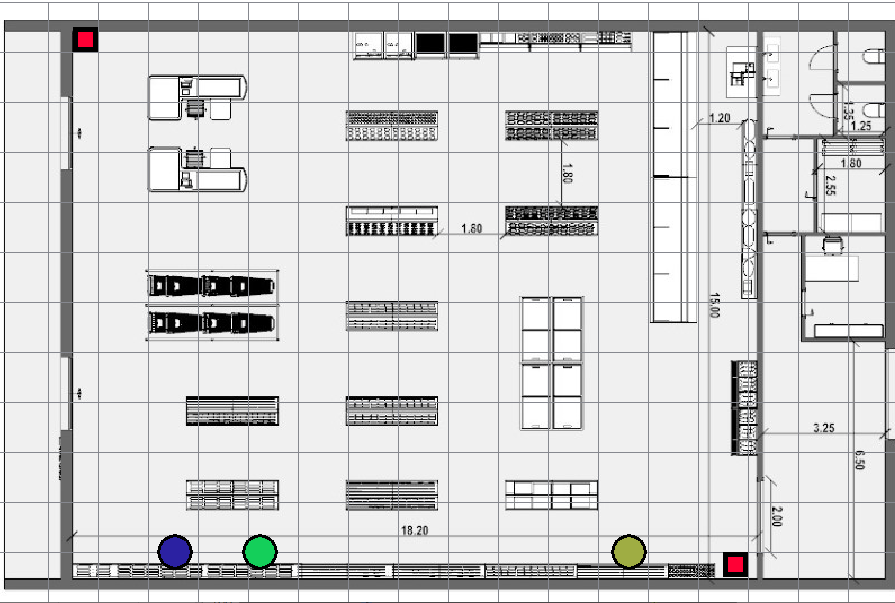
Technical project/Memmory/images/supermarket_1.PNG
