RarceD/TFM--Bluetooth-Beacon-Tracking-/Technical project/Memmory/images/supermarket_2.PNG

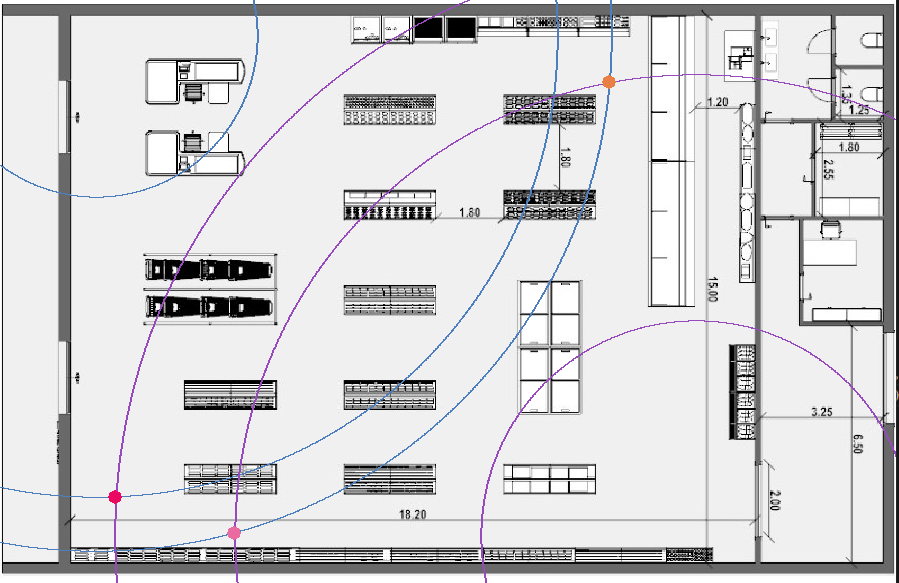
Technical project/Memmory/images/supermarket_2.PNG
