RarceD/TFM--Bluetooth-Beacon-Tracking-/Technical project/Memmory/images/tipos_beacon_altbeacon.PNG

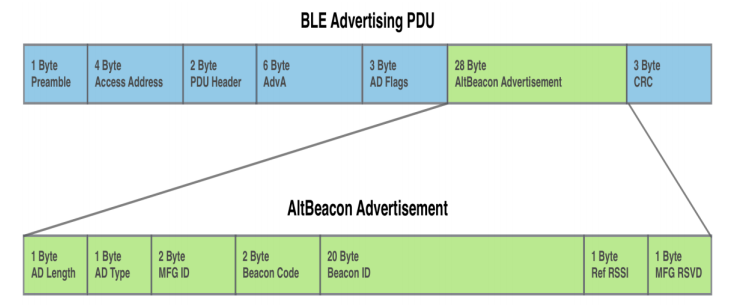
Technical project/Memmory/images/tipos_beacon_altbeacon.PNG
