RarceD/TFM--Bluetooth-Beacon-Tracking-/Technical project/Memmory/images/trilateration_ajustments_2.png

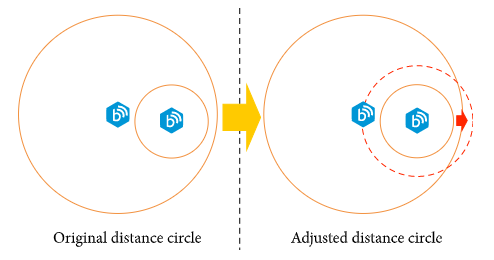
Technical project/Memmory/images/trilateration_ajustments_2.png
