RarceD/TFM--Bluetooth-Beacon-Tracking-/Technical project/Memmory/images/trilateration_ajustments_3.png

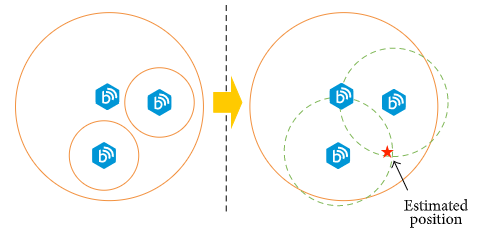
Technical project/Memmory/images/trilateration_ajustments_3.png
