RarceD/TFM--Bluetooth-Beacon-Tracking-/Technical project/Memmory/images/trilateration_ajustments_4.png

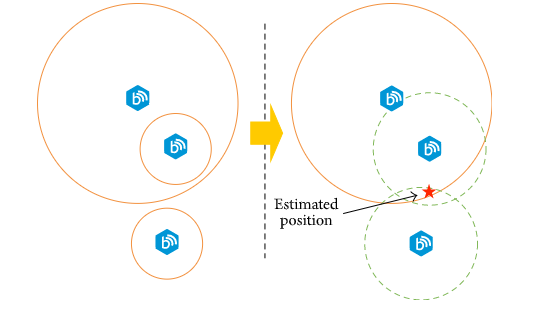
Technical project/Memmory/images/trilateration_ajustments_4.png
