RarceD/TFM--Bluetooth-Beacon-Tracking-/Technical project/Schematics/antennas_variety.jpeg

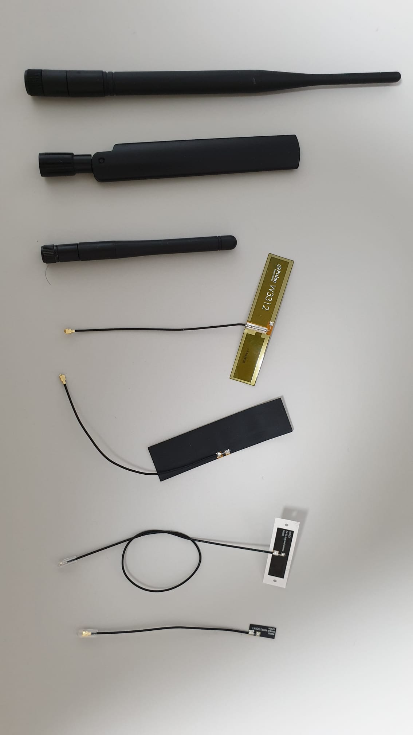
Technical project/Schematics/antennas_variety.jpeg
