RarceD/TFM--Bluetooth-Beacon-Tracking-/Technical project/Schematics/Beacon_Listener_v2.0/duck.jpg

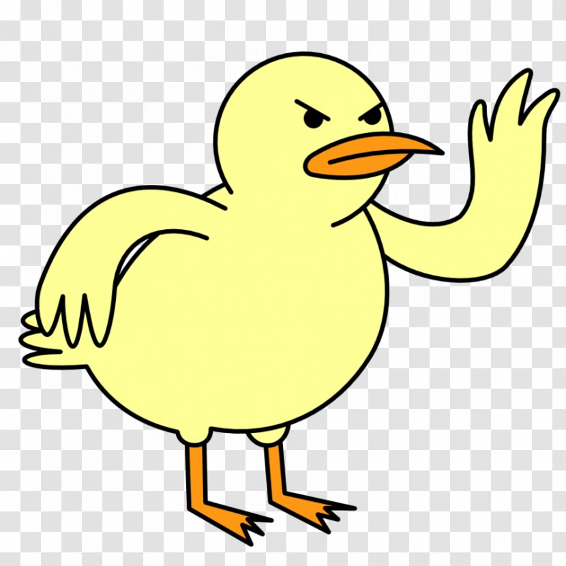
Technical project/Schematics/Beacon_Listener_v2.0/duck.jpg
