RarceD/TFM--Bluetooth-Beacon-Tracking-/Technical project/Schematics/emiter_uC.PNG

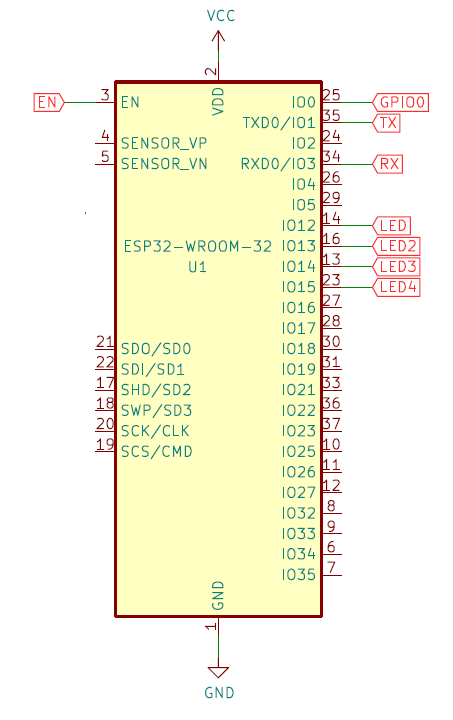
Technical project/Schematics/emiter_uC.PNG
