RarceD/TFM--Bluetooth-Beacon-Tracking-/Technical project/Memmory/draws_linked.pdf

# Rubén Control ¹⁶ 12 10.2

Dept.; Technical reference; Created by; Approved by; Document type; Document status; Aprobado

Title BeaconNode | DWG No. Escala 1:1

Rev. | Date of issue | Sheet 1/1

70

Dept.; Technical reference; Created by; Approved by; Document type; Document status; Rubén Control; Ø5 Ø3 Escala 1:1

Title BeaconListener | DWG No.

Rev. | Date of issue | Sheet 1/1
